JingYang1124/HEX-LINK/firmware/ArduinoIDE_Proj/Additional_Libraries/Mirf/MirfHardwareSpiDriver.cpp

#include "MirfHardwareSpiDriver.h"
uint8_t MirfHardwareSpiDriver::transfer(uint8_t data){
	return SPI.transfer(data);
}

void MirfHardwareSpiDriver::begin(){
	SPI.begin();
	SPI.setDataMode(SPI_MODE0);
	SPI.setClockDivider(SPI_2XCLOCK_MASK);
}

void MirfHardwareSpiDriver::end(){
}

MirfHardwareSpiDriver MirfHardwareSpi;
