JingYang1124/HEX-LINK/firmware/ArduinoIDE_Proj/Additional_Libraries/Mirf/MirfHardwareSpiDriver.h

#include "MirfSpiDriver.h"

#ifndef __MIRF_HARDWARE_SPI_DRIVER
#define __MIRF_HARDWARE_SPI_DRIVER 

#include <SPI.h>

class MirfHardwareSpiDriver : public MirfSpiDriver {

	public: 
		virtual uint8_t transfer(uint8_t data);
		virtual void begin();
		virtual void end();
};

extern MirfHardwareSpiDriver MirfHardwareSpi;

#endif
