JingYang1124/HEX-LINK/firmware/ArduinoIDE_Proj/Additional_Libraries/Mirf/MirfSpiDriver.h

#ifndef __MIRF_SPI_DRIVER
#define __MIRF_SPI_DRIVER

extern "C" {
	#include <string.h>
	#include <inttypes.h>
}

class MirfSpiDriver {
	public:
		virtual uint8_t transfer(uint8_t data);

		virtual void begin();
		virtual void end();
};

#endif
