JingYang1124/HEX-LINK/firmware/ArduinoIDE_Proj/Additional_Libraries/Adafruit_SSD1306/splash.h

#define splash1_width 82
#define splash1_height 64

const uint8_t PROGMEM splash1_data[] = {
    B00000000, B00000000, B00000000, B00000000, B00000000, B00000001, B10000000,
    B00000000, B00000000, B00000000, B00000000, B00000000, B00000000, B00000000,
    B00000000, B00000000, B00000011, B10000000, B00000000, B00000000, B00000000,
    B00000000, B00000000, B00000000, B00000000, B00000000, B00000000, B00000111,
    B11000000, B00000000, B00000000, B00000000, B00000000, B00000000, B00000000,
    B00000000, B00000000, B00000000, B00000111, B11000000, B00000000, B00000000,
    B00000000, B00000000, B00000000, B00000000, B00000000, B00000000, B00000000,
    B00001111, B11000000, B00000000, B00000000, B00000000, B00000000, B00000000,
    B00000000, B00000000, B00000000, B00000000, B00011111, B11100000, B00000000,
    B00000000, B00000000, B00000000, B00000000, B00000000, B00000000, B00000000,
    B00000000, B00011111, B11100000, B00000000, B00000000, B00000000, B00000000,
    B00000000, B00000000, B00000000, B00000000, B00000000, B00111111, B11100000,
    B00000000, B00000000, B00000000, B00000000, B00000000, B00000000, B00000000,
    B00000000, B00000000, B00111111, B11110000, B00000000, B00000000, B00000000,
    B00000000, B00000000, B00000000, B00000000, B00000000, B00000000, B01111111,
    B11110000, B00000000, B00000000, B00000000, B00000000, B00000000, B00000000,
    B00000000, B00011111, B11111000, B01111111, B11110000, B00000000, B00000000,
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
  B00000000,B00000000,B00000000,B00000000,B00000000,B00000000,B00000000,B00000000,B00000000,B00000000,B00000000,B00000000,B00000000,B00000000,B00000000,
};
