JingYang1124/HEX-LINK/firmware/ArduinoIDE_Proj/Hex_Link_Leonardo/MainFunction.h

#ifndef MAINFUNCTION_H
#define MAINFUNCTION_H

#include "Universal_Headers.h"
#include "Keyboard.h"
#include "Mouse.h"
#include "LED.h"
#include "COM.h"
#include "RTE.h"
#include "OLED.h"

extern void Init_Setup(void);

extern void Loop_Function(void);


#endif
