JingYang1124/HEX-LINK/firmware/ArduinoIDE_Proj/Hex_Link_Nano/MainFunction.h

#ifndef MAINFUNCTION_H
#define MAINFUNCTION_H

#include "Universal_Headers.h"
#include "IMU.h"
#include "ISR.h"
#include "LED.h"
#include "COM.h"
#include "ASW.h"
#include "Filter.h"

extern void Init_Setup(void);

extern void Loop_Function(void);


#endif
