JingYang1124/HEX-LINK/firmware/ArduinoIDE_Proj/Hex_Link_Leonardo/ASW.h

#ifndef ASW_H
#define ASW_H
#include "Universal_Headers.h"
#include "COM.h"
#include "Keyboard.h"
#include "Mouse.h"

extern void ASW_NRF_RECEIVE(void);
extern void ASW_KEYBOARD_SEND(void);
extern void ASW_DEVICE_CONFIRM(void);

#endif
