JingYang1124/HEX-LINK/firmware/ArduinoIDE_Proj/Hex_Link_Leonardo/Device_Cfg.h

#ifndef DEVICE_CONFIG_H
#define DEVICE_CONFIG_H

#include "Universal_Headers.h"

/*Debug Definitions*/
//#define RTE_TASK_SERIAL_PRINT   

/*NRF PIN Define*/
#define NRF_CE_PIN  8
#define NRF_CSN_PIN 7

/*LED PIN Define*/
#define LED_PIN   13

#define DeviceTypeNum  7




#endif
