JingYang1124/HEX-LINK/firmware/ArduinoIDE_Proj/Hex_Link_Leonardo/LED.cpp

#include "LED.h"
#include "Device_Cfg.h"
void LED_Init(void){
	pinMode(LED_PIN,OUTPUT);
}

void LED_Light(void){
  digitalWrite(LED_PIN, HIGH); 
}

void LED_Light_Off(void){
	digitalWrite(LED_PIN, LOW); 
}
