JingYang1124/HEX-LINK/firmware/ArduinoIDE_Proj/Hex_Link_Nano/ASW.h

#ifndef ASW_H
#define ASW_H


extern void ASW_Loop(void);

extern void ASW_CHEST(void);
extern void ASW_LEFT_ARM(void);
extern void ASW_RIGHT_ARM(void);
extern void ASW_LEFT_LEG(void);
extern void ASW_RIGHT_LEG(void);
extern void ASW_WEAPON(void);
extern void ASW_TOOL(void);
extern void ASW_TEST(void);
extern void ASW_Send_Command(void);

#endif
