JingYang1124/HEX-LINK/firmware/ArduinoIDE_Proj/Hex_Link_Nano/Device_Cfg.cpp

#include "Universal_Headers.h"
#include "Device_Cfg.h"


/*
  DEVICE_CHEST,
  DEVICE_LEFT_ARM,
  DEVICE_RIGHT_ARM,
  DEVICE_LEFT_LEG,
  DEVICE_TOOL,
  DEVICE_RIGHT_LEG,
  DEVICE_WEAPON,
  DEVICE_TEST
*/

DeviceIdType DeviceId = DEVICE_LEFT_LEG;
